berin-aquaquad/orange-pi-5/Cad drawing/gcode/steel bracket cnc cut out.jpg

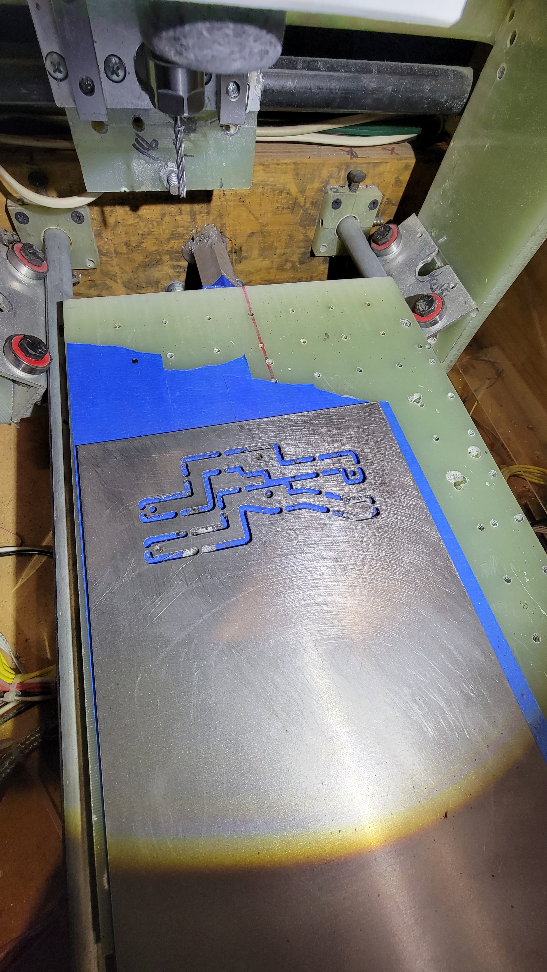
Cad drawing/gcode/steel bracket cnc cut out.jpg
