berin-aquaquad/orange-pi-5/design concept pipeline/20230228_231935.jpg

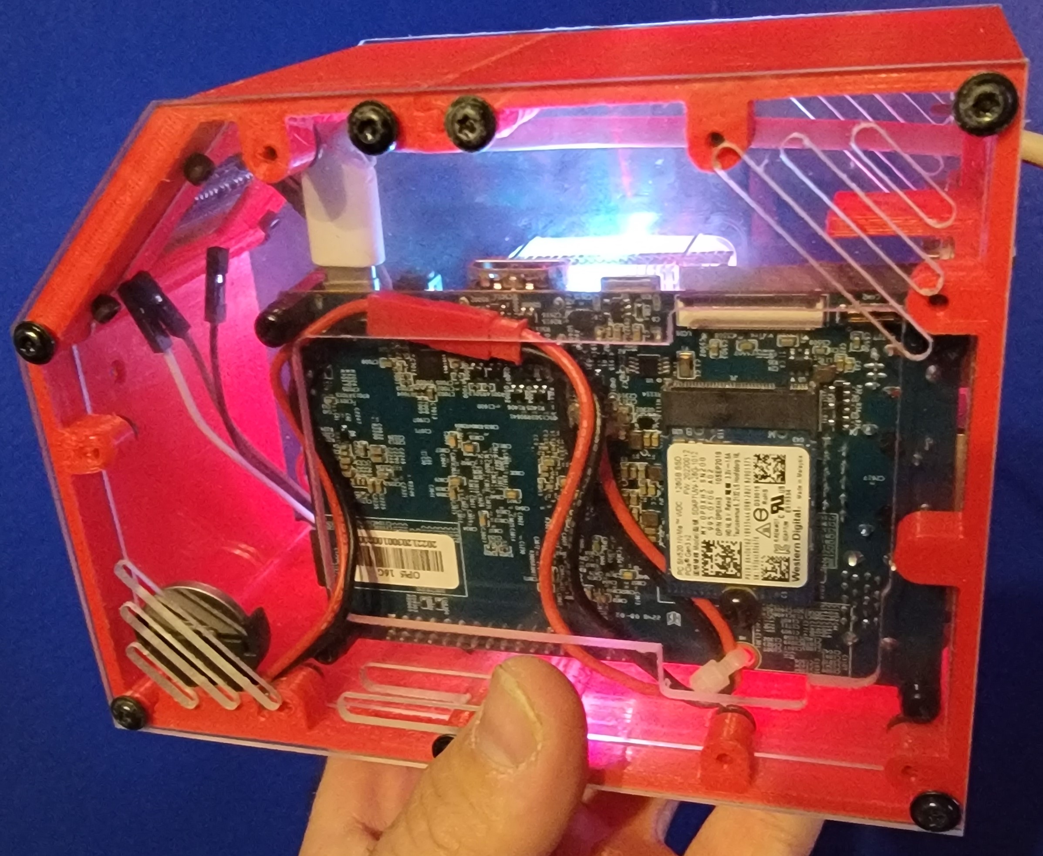
design concept pipeline/20230228_231935.jpg
