berin-aquaquad/orange-pi-5/design concept pipeline/20230228_231943.jpg

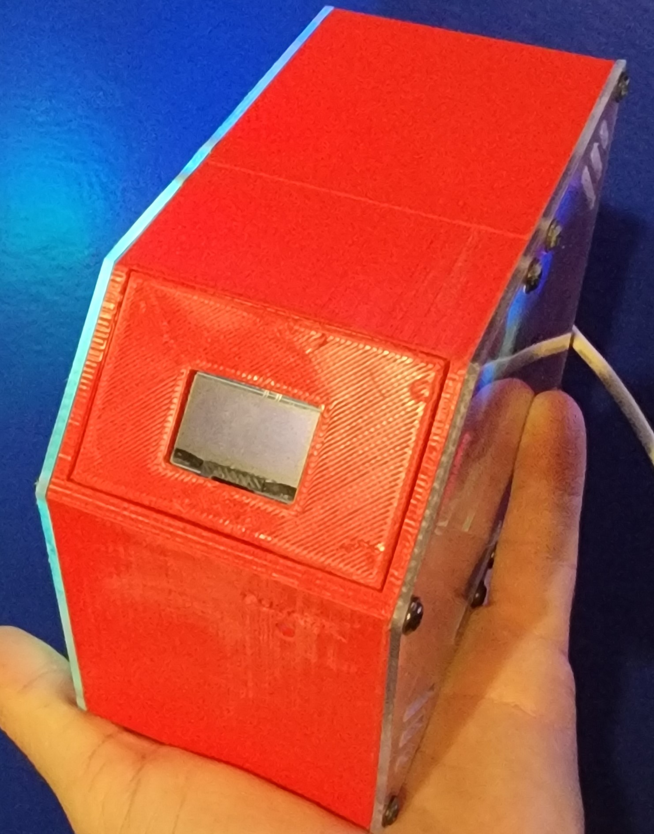
design concept pipeline/20230228_231943.jpg
