berin-aquaquad/orange-pi-5/front side.jpg

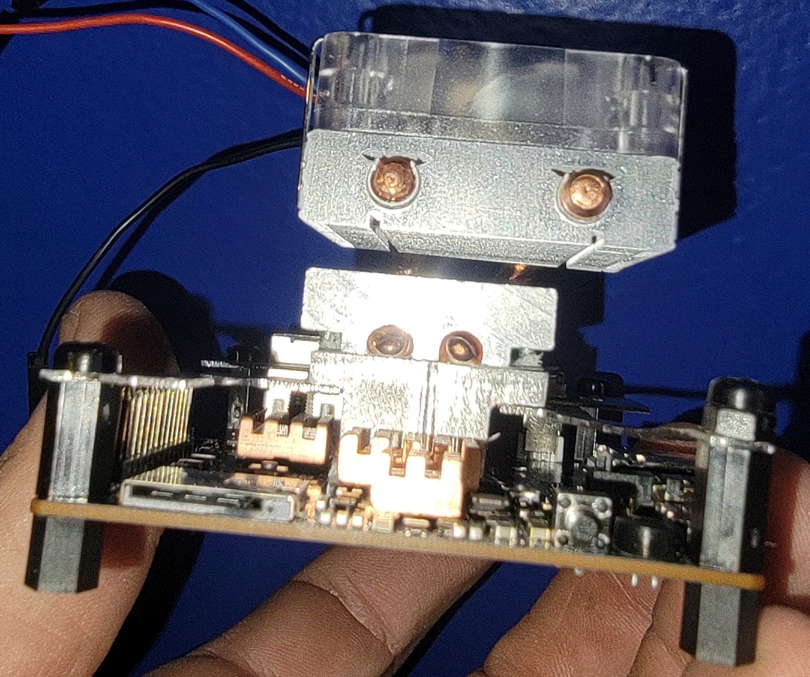
front side.jpg
