berin-aquaquad/orange-pi-5/left corner forward.jpg

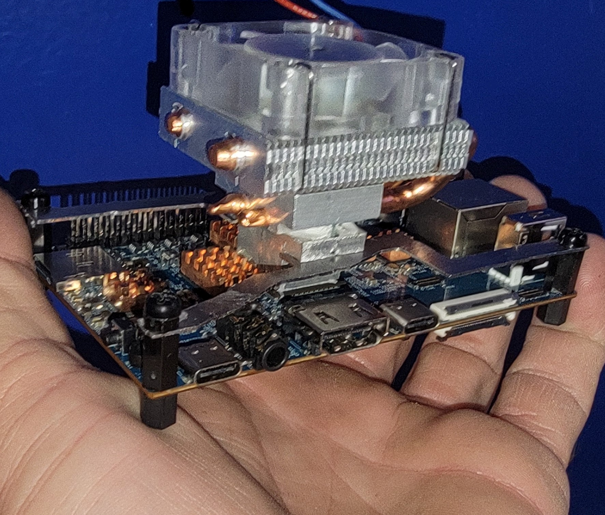
left corner forward.jpg
