berin-aquaquad/orange-pi-5/opi5 micro desktop back right.jpg

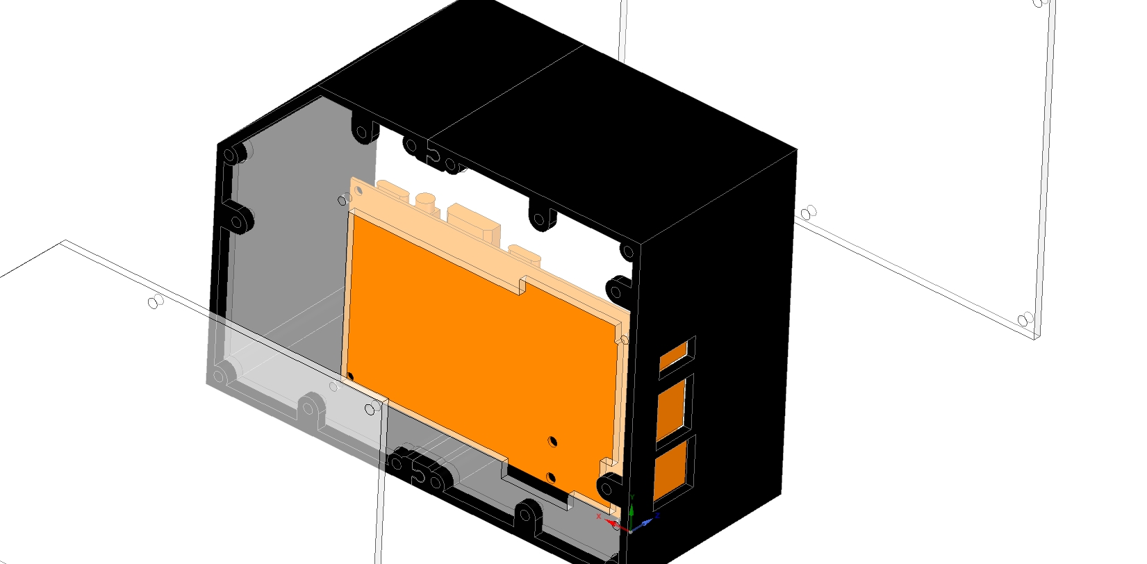
opi5 micro desktop back right.jpg
