berin-aquaquad/orange-pi-5/opi5 micro desktop front left.jpg

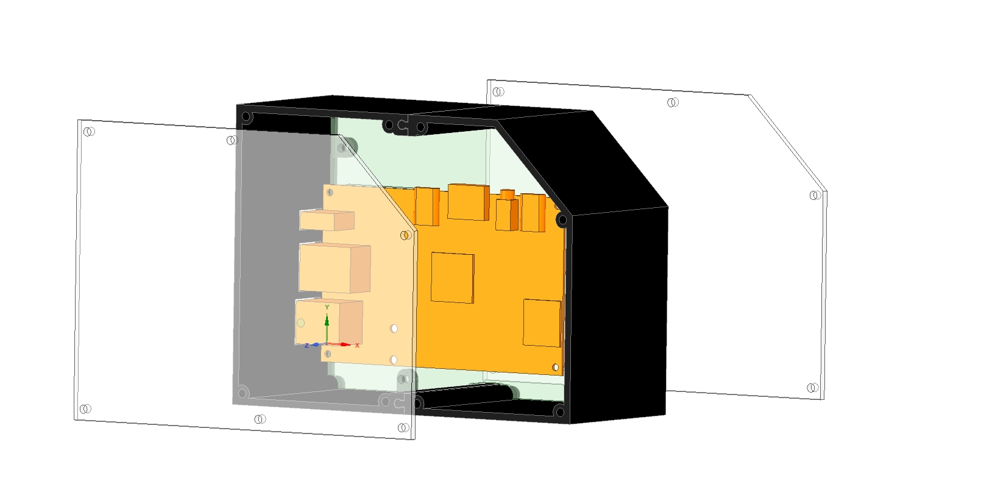
opi5 micro desktop front left.jpg
