berin-aquaquad/orange-pi-5/opi5 micro desktop heatsink standoff mount bracket.jpg

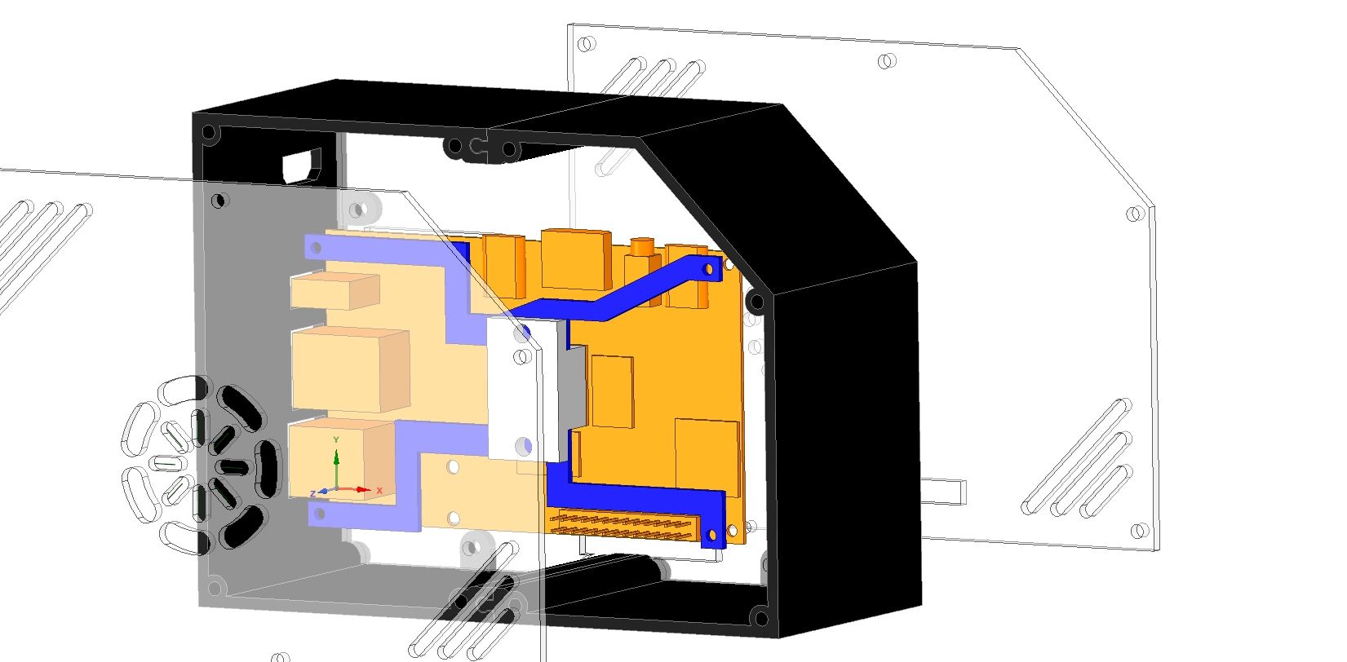
opi5 micro desktop heatsink standoff mount bracket.jpg
