berin-aquaquad/orange-pi-5/opi5 micro desktop heatsink standoff.jpg

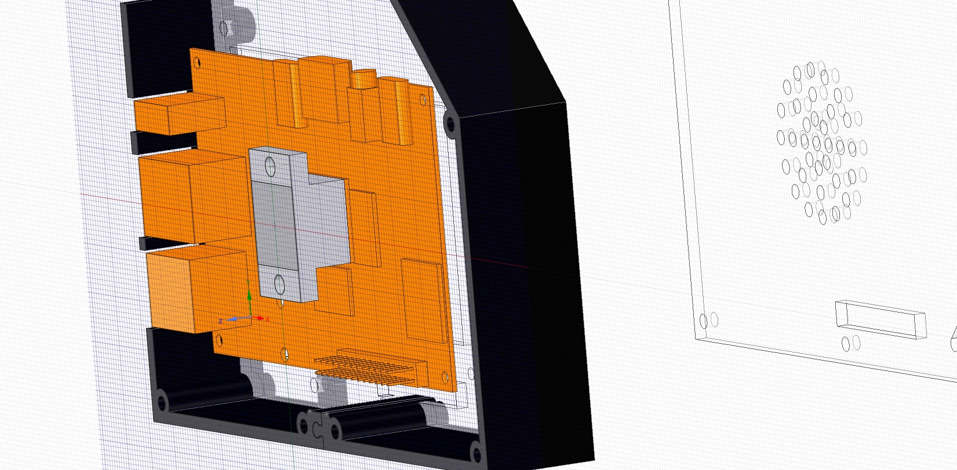
opi5 micro desktop heatsink standoff.jpg
