berin-aquaquad/orange-pi-5/opi5 micro desktop with out SBC.jpg

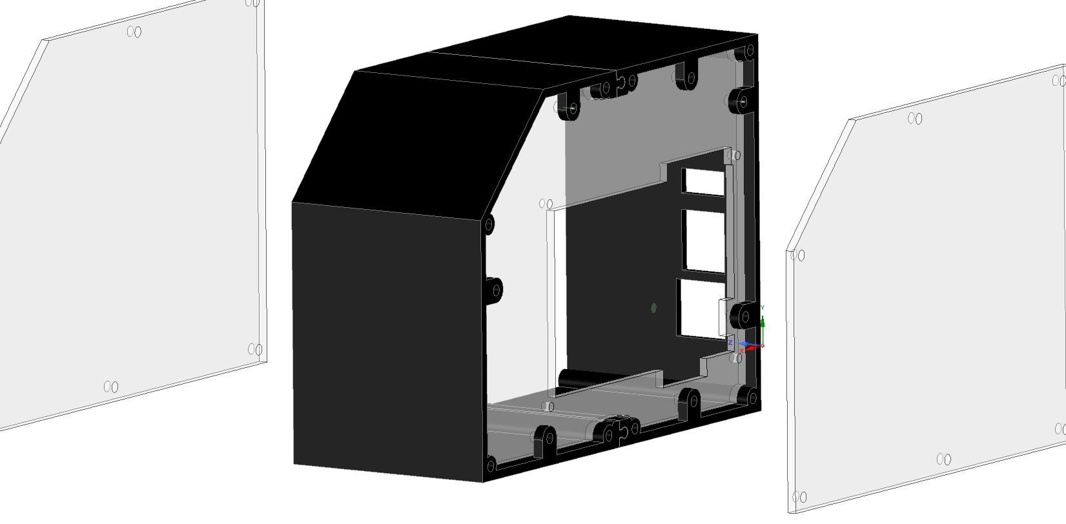
opi5 micro desktop with out SBC.jpg
